gerryvel/Yacht-V3/Bilder/photo_2025-11-05_21-48-31.jpg

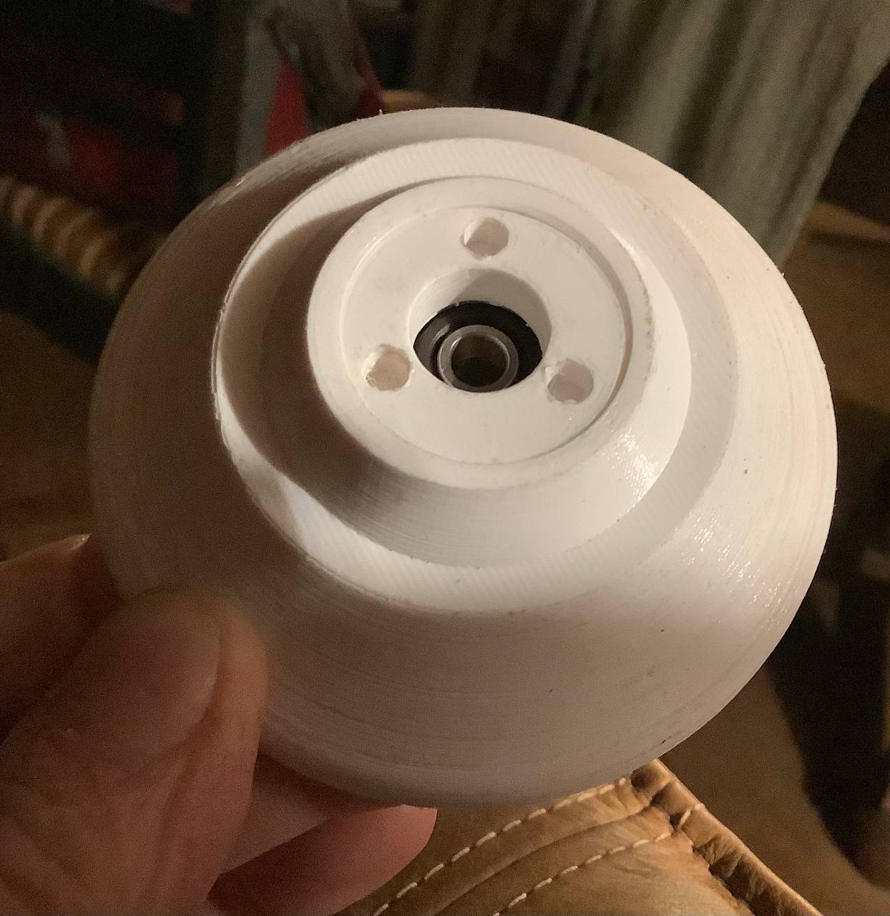
Bilder/photo_2025-11-05_21-48-31.jpg
