gerryvel/Yacht-V3/Bilder/photo_2025-11-09_20-17-32.jpg

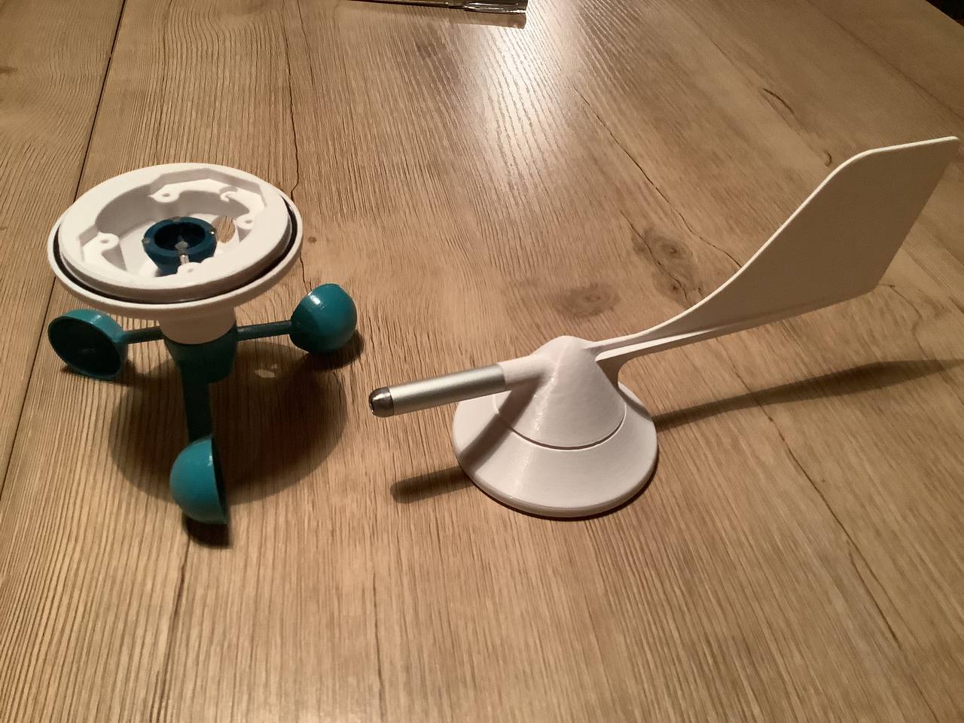
Bilder/photo_2025-11-09_20-17-32.jpg
