gerryvel/Yacht-V3/Bilder/photo_2025-11-09_20-17-37.jpg

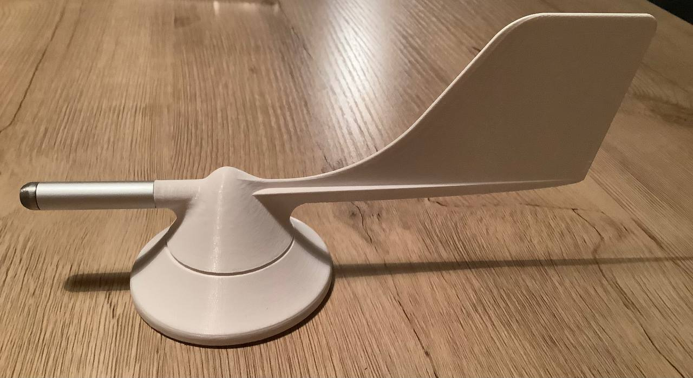
Bilder/photo_2025-11-09_20-17-37.jpg
