gerryvel/Yacht-V3/Bilder/photo_2025-11-09_20-17-39.jpg

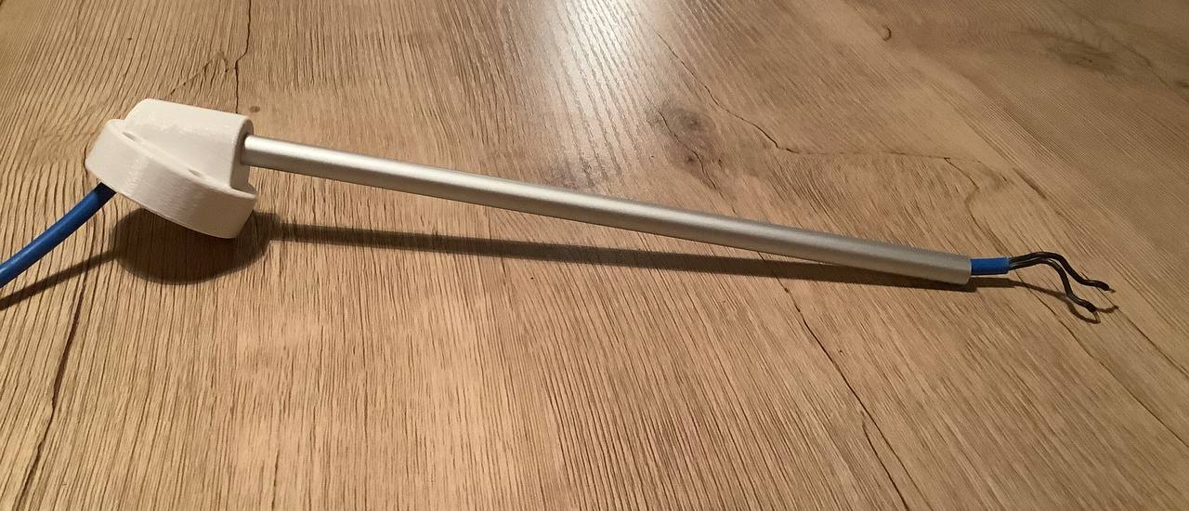
Bilder/photo_2025-11-09_20-17-39.jpg
